plastibot/citro/images/Citro6_32.png

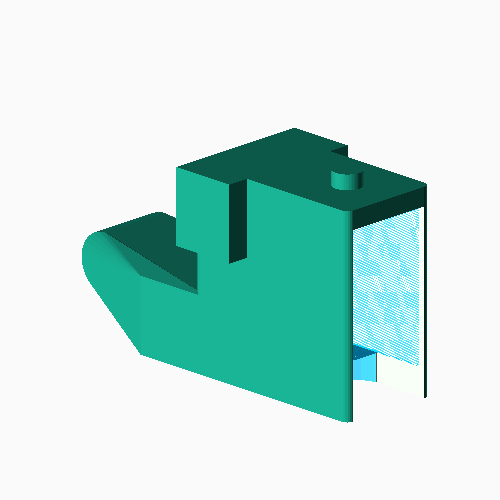
images/Citro6_32.png
