plastibot/citro/images/Citro6_33.png

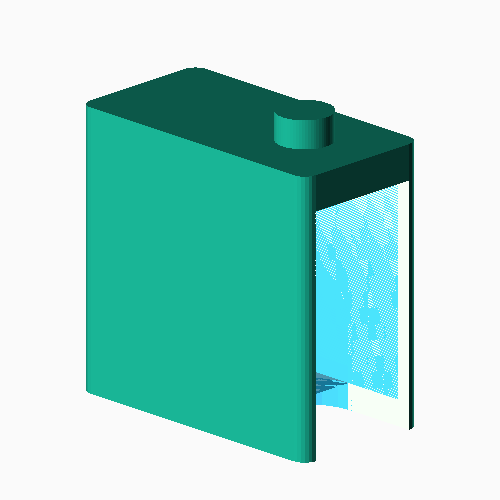
images/Citro6_33.png
