plastibot/citro/images/servo_5g.png

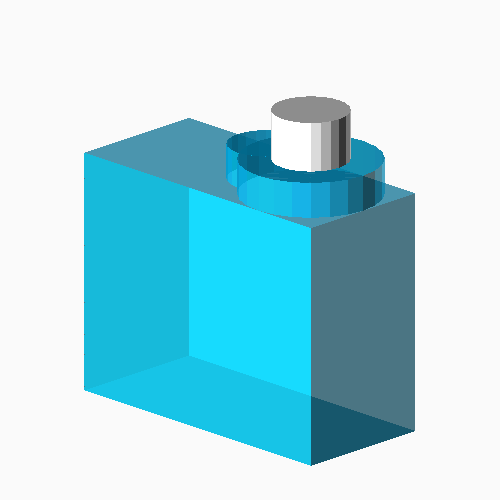
images/servo_5g.png
