plastibot/citro/stl/wemos_d1_mini_pro_board.stl

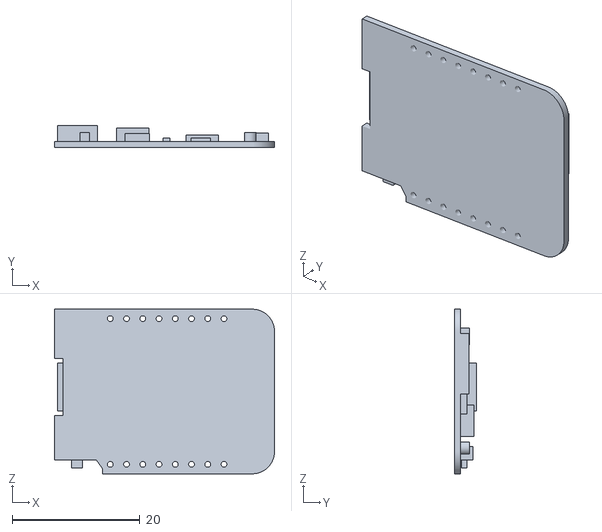
[picture p86: CAD file, 2018-08-11]
stl/wemos_d1_mini_pro_board.stl
34.4 x 3.50 x 25.7
