plastibot/citro/MiniPlan6/MiniPlan6_61R.stl

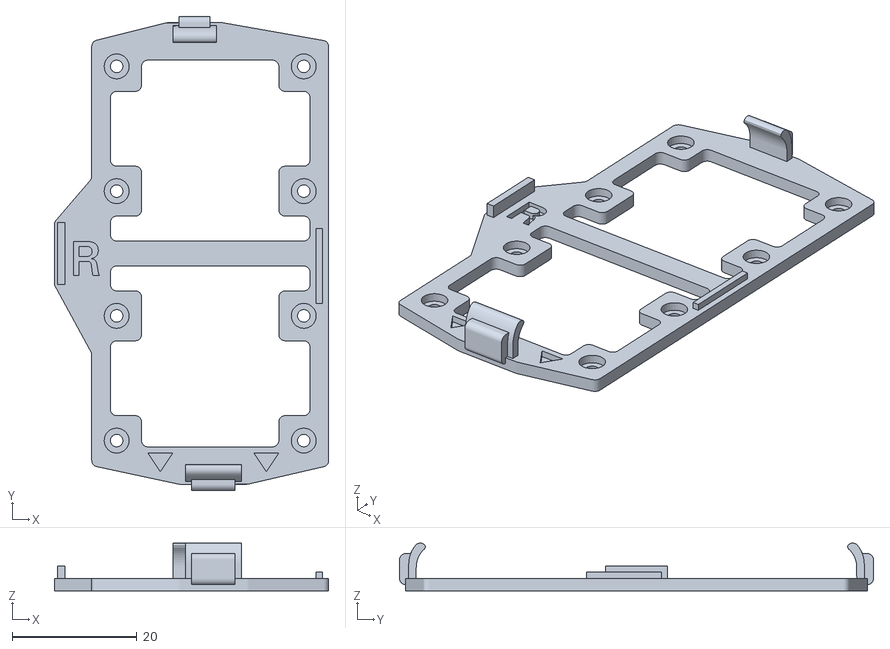
[picture p87: CAD file, 2017-10-25]
MiniPlan6/MiniPlan6_61R.stl
44.0 x 76.0 x 7.67
