plastibot/citro/stl/electronics_pca9685.stl

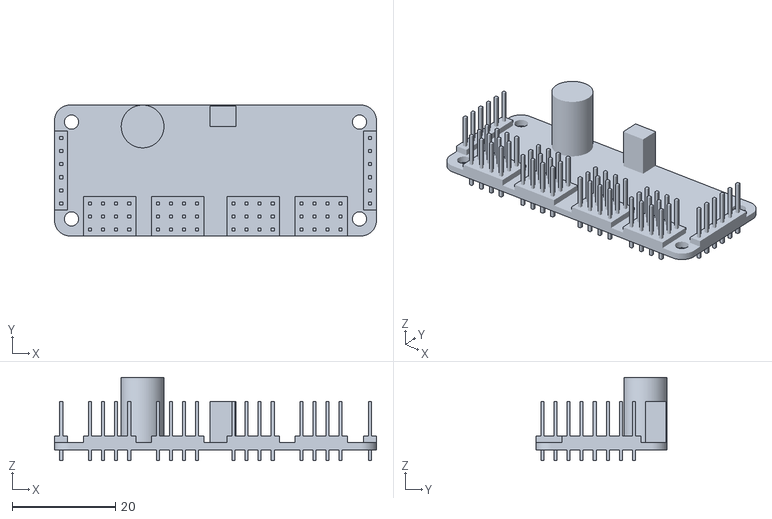
[picture p88: CAD file, 2017-10-30]
stl/electronics_pca9685.stl
62.5 x 25.4 x 16.2
