plastibot/citro/MiniPlan6/MiniPlan6_60.stl

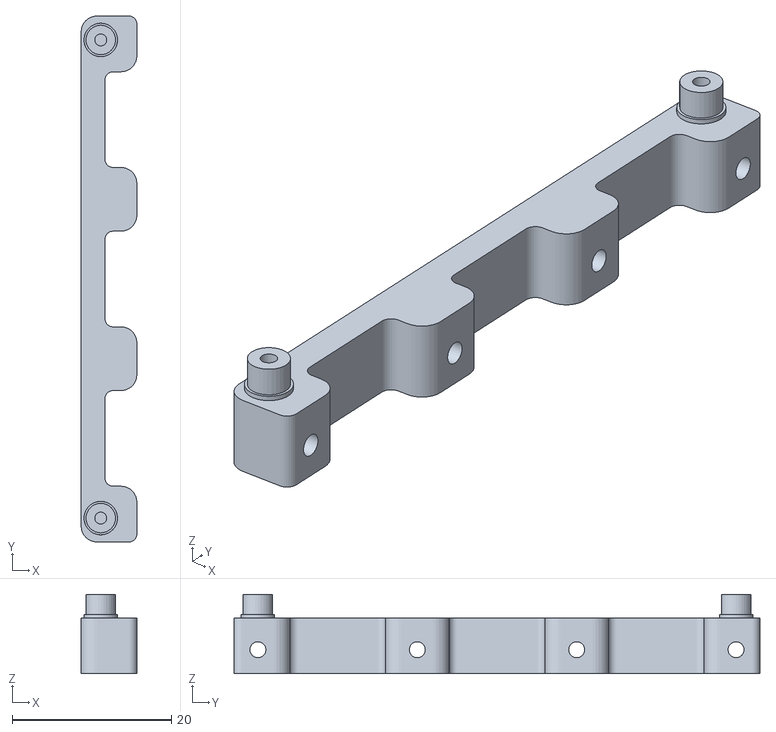
[picture p89: CAD file, 2017-10-25]
MiniPlan6/MiniPlan6_60.stl
7.00 x 66.0 x 9.95
