plastibot/citro/MiniPlan6/MiniPlan6_43R.stl

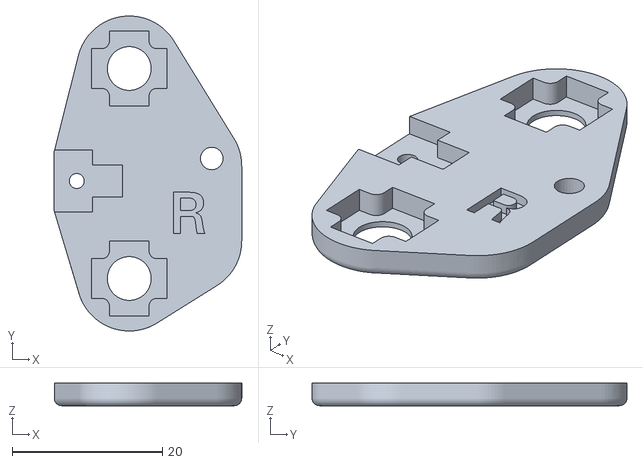
[picture p90: CAD file, 2017-10-25]
MiniPlan6/MiniPlan6_43R.stl
25.0 x 42.0 x 3.00
