plastibot/citro/stl/Citro6_32.stl

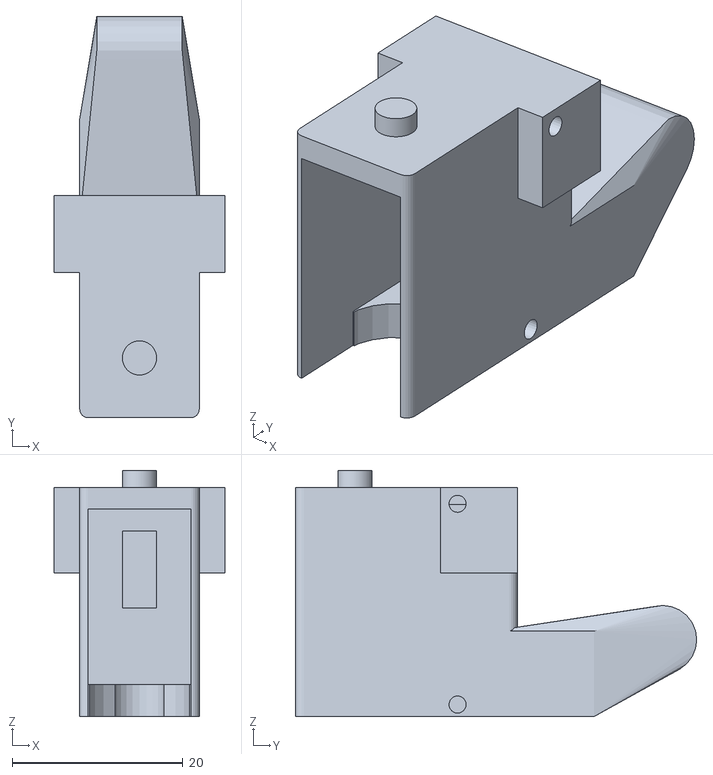
[picture p91: CAD file, 2017-10-30]
stl/Citro6_32.stl
20.0 x 47.0 x 28.8
