plastibot/citro/stl/Citro6_43L.stl

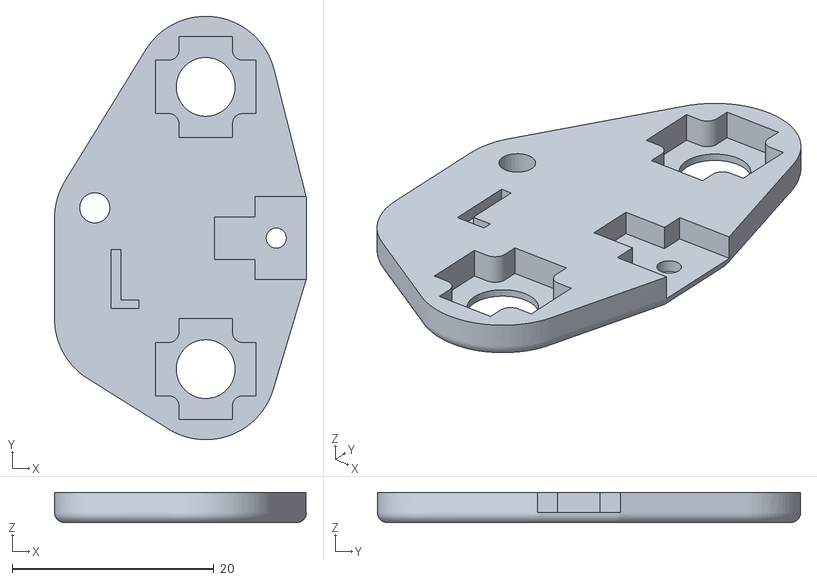
[picture p92: CAD file, 2017-10-30]
stl/Citro6_43L.stl
25.0 x 42.0 x 3.00
