plastibot/citro/MiniPlan6/MiniPlan6_45L.stl

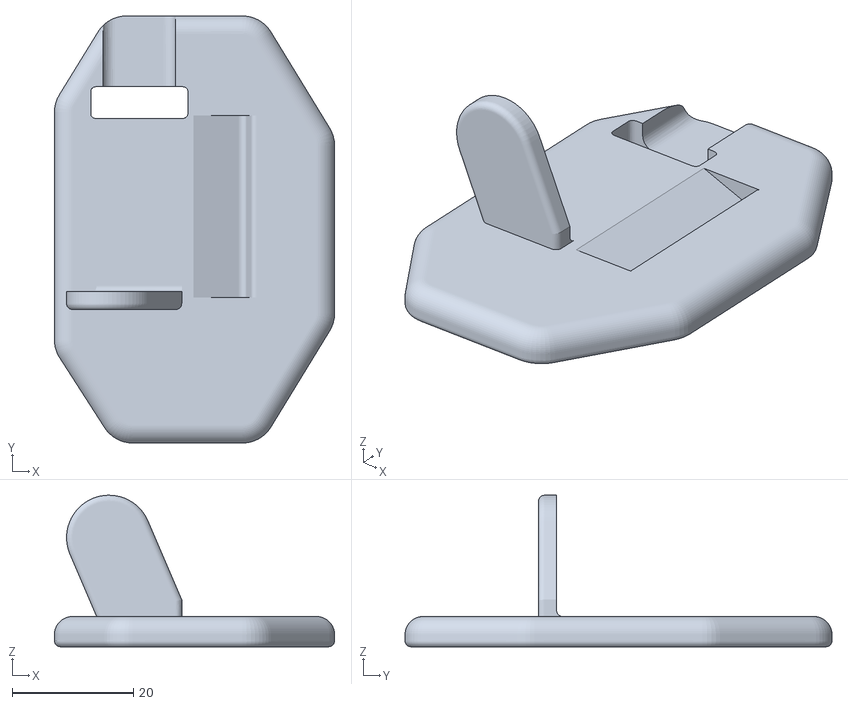
[picture p93: CAD file, 2017-10-25]
MiniPlan6/MiniPlan6_45L.stl
46.2 x 70.4 x 25.0
