plastibot/citro/MiniPlan6/MiniPlan6_40D.stl

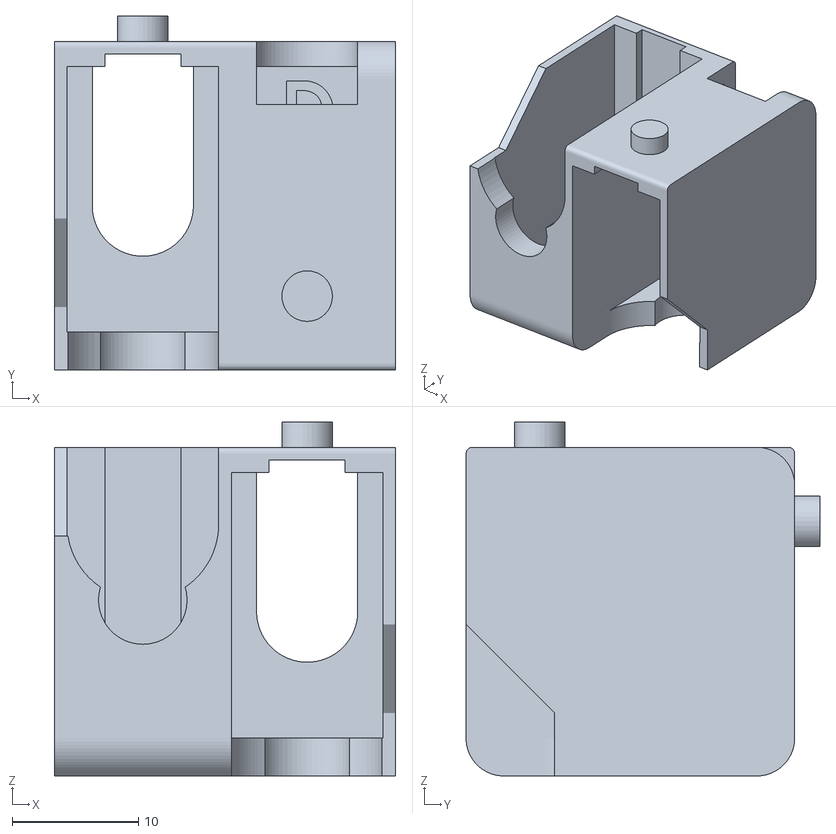
[picture p94: CAD file, 2017-10-25]
MiniPlan6/MiniPlan6_40D.stl
27.0 x 28.0 x 28.0
