plastibot/citro/stl/Citro6_50.stl

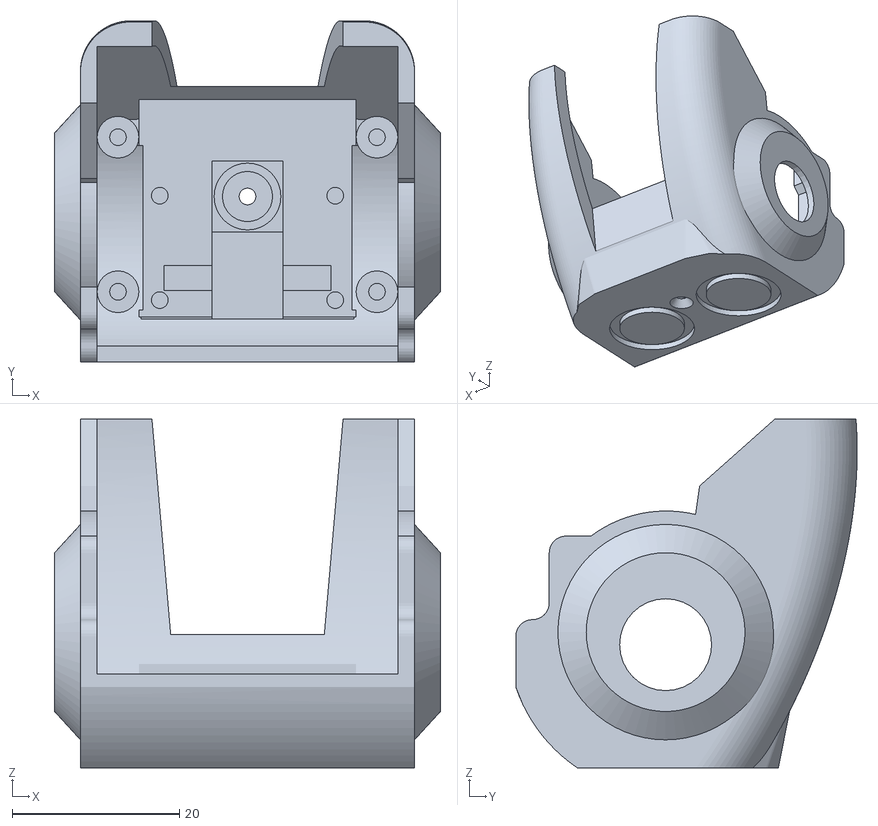
[picture p95: CAD file, 2017-10-30]
stl/Citro6_50.stl
46.2 x 40.9 x 41.8
