plastibot/citro/stl/Citro6_20.stl

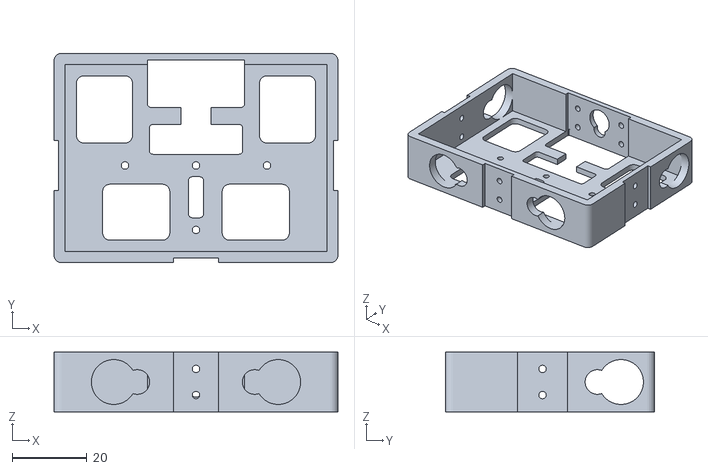
[picture p96: CAD file, 2017-10-30]
stl/Citro6_20.stl
76.0 x 56.0 x 16.0
