plastibot/citro/MiniPlan6/MiniPlan6_70.stl

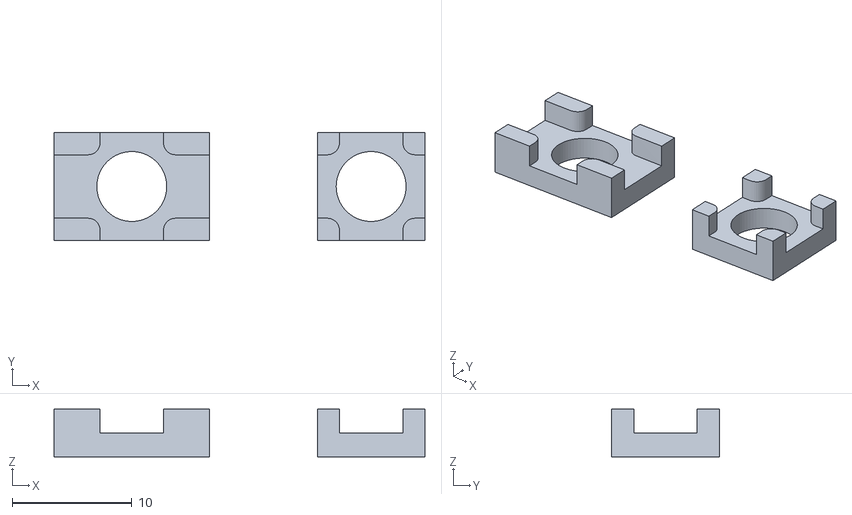
[picture p97: CAD file, 2017-10-25]
MiniPlan6/MiniPlan6_70.stl
31.0 x 9.00 x 4.00
