plastibot/citro/MiniPlan6/MiniPlan5_40.stl

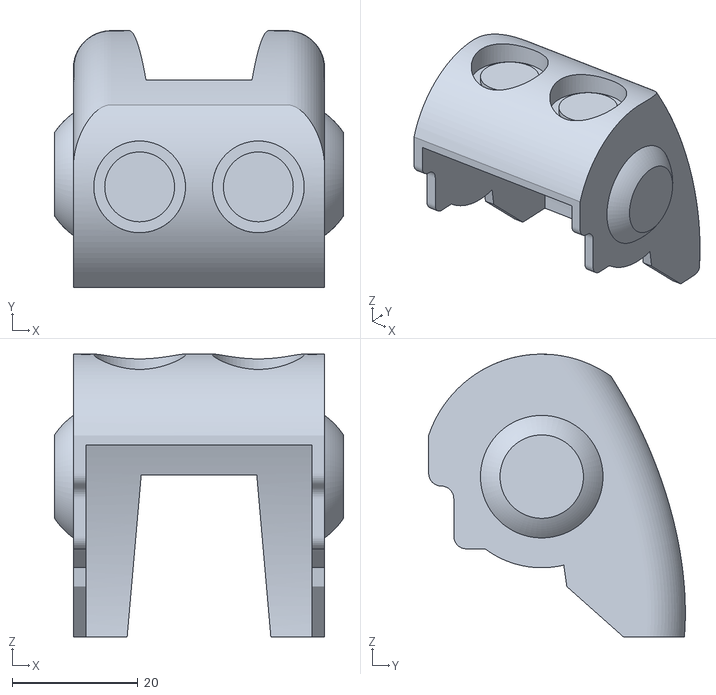
[picture p98: CAD file, 2017-10-25]
MiniPlan6/MiniPlan5_40.stl
46.0 x 40.9 x 45.0
