plastibot/citro/stl/Citro6_51.stl

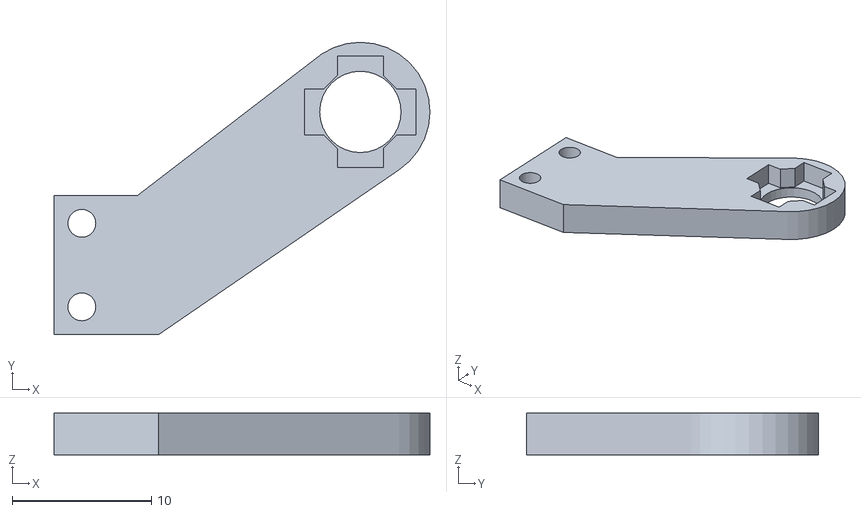
[picture p99: CAD file, 2017-10-30]
stl/Citro6_51.stl
27.0 x 21.0 x 3.00
