plastibot/citro/stl/Citro6_33.stl

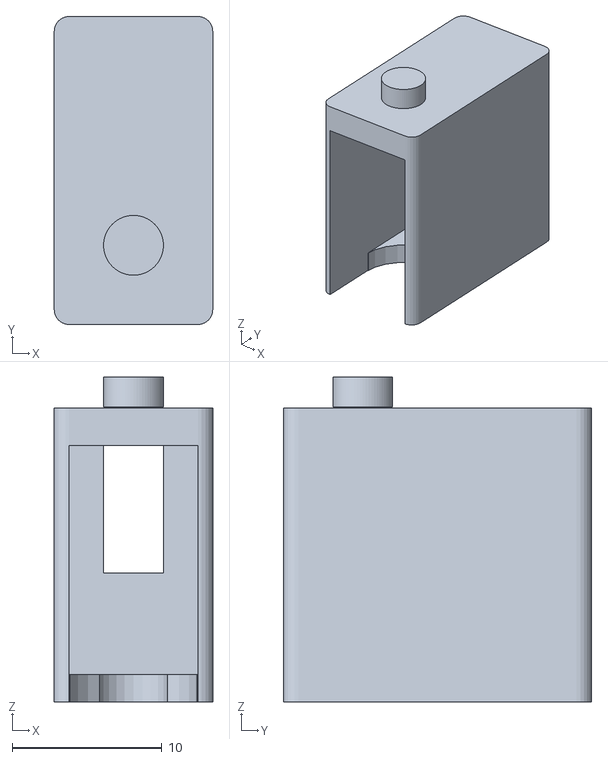
[picture p100: CAD file, 2017-10-30]
stl/Citro6_33.stl
10.6 x 20.6 x 21.7
