plastibot/citro/MiniPlan6/MiniPlan6_30.stl

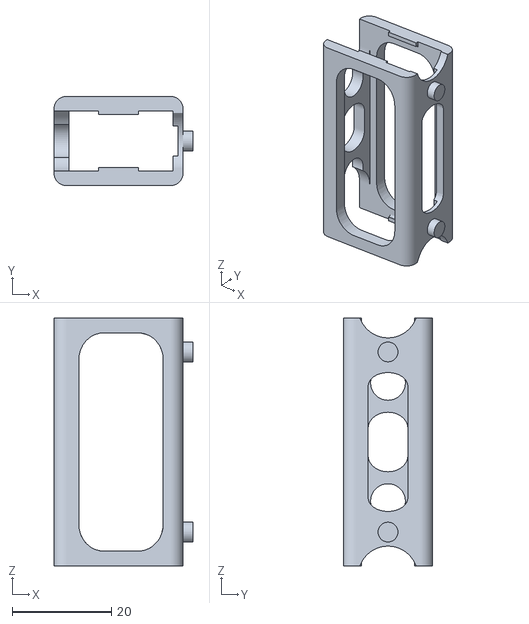
[picture p101: CAD file, 2017-10-25]
MiniPlan6/MiniPlan6_30.stl
28.0 x 18.0 x 50.0
