plastibot/citro/stl/Citro6_40B.stl

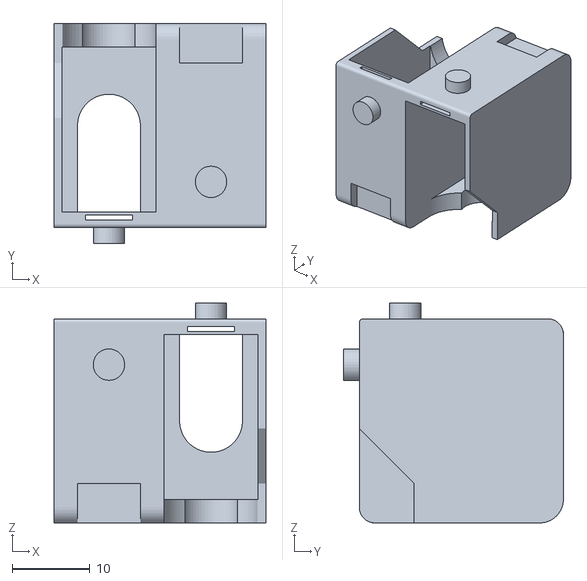
[picture p102: CAD file, 2017-10-30]
stl/Citro6_40B.stl
27.3 x 28.3 x 28.3
