plastibot/citro/stl/Citro6_12B.stl

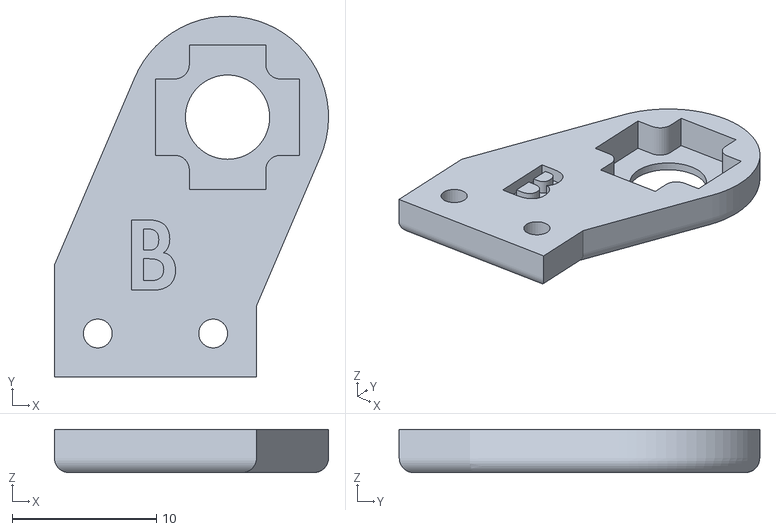
[picture p103: CAD file, 2017-10-30]
stl/Citro6_12B.stl
19.0 x 25.0 x 3.00
