plastibot/citro/stl/Citro6_26.stl

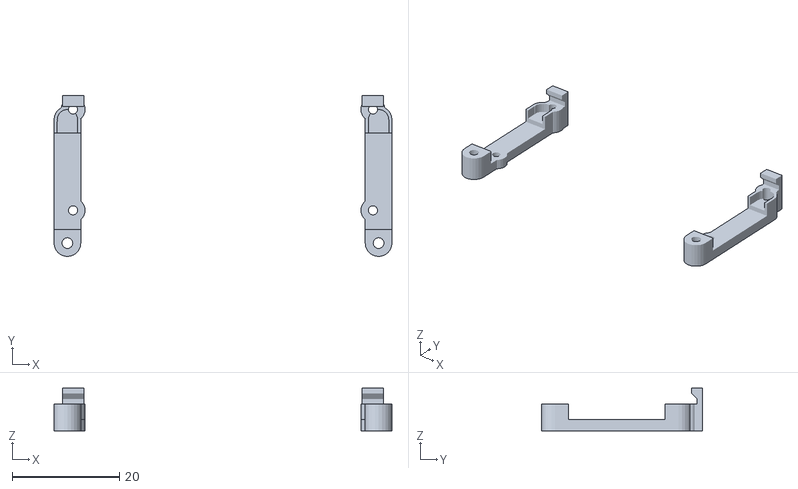
[picture p104: CAD file, 2017-10-30]
stl/Citro6_26.stl
63.0 x 30.0 x 8.00
