plastibot/citro/stl/Citro6_22.stl

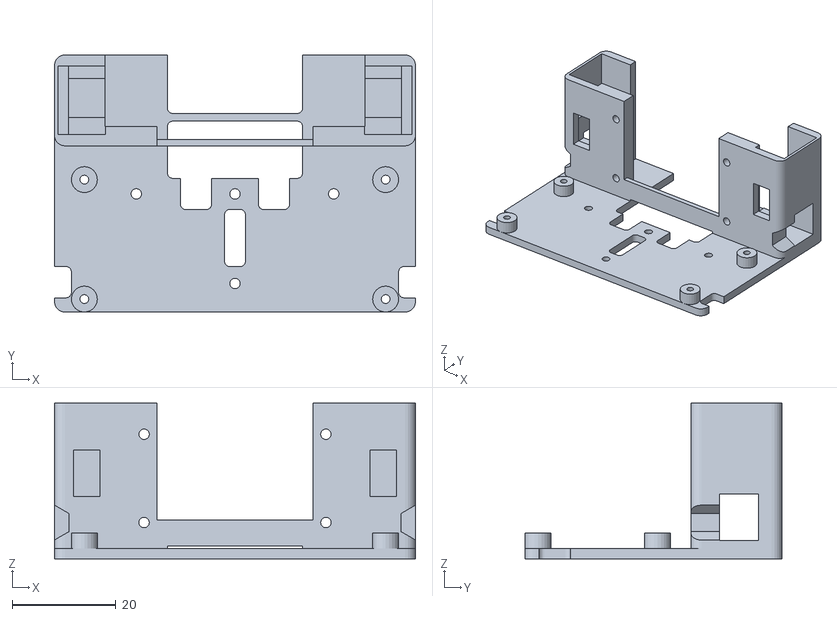
[picture p105: CAD file, 2017-10-30]
stl/Citro6_22.stl
69.5 x 49.5 x 30.0
