plastibot/citro/stl/servo_5g.stl

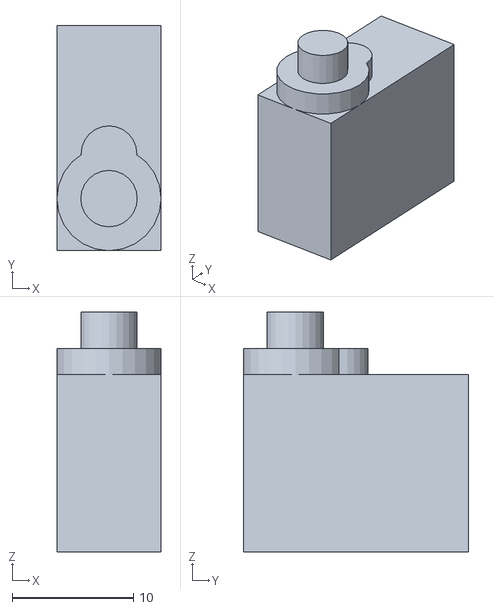
[picture p106: CAD file, 2017-10-30]
stl/servo_5g.stl
8.60 x 18.6 x 19.8
