plastibot/citro/stl/electronics_PiCamera.stl

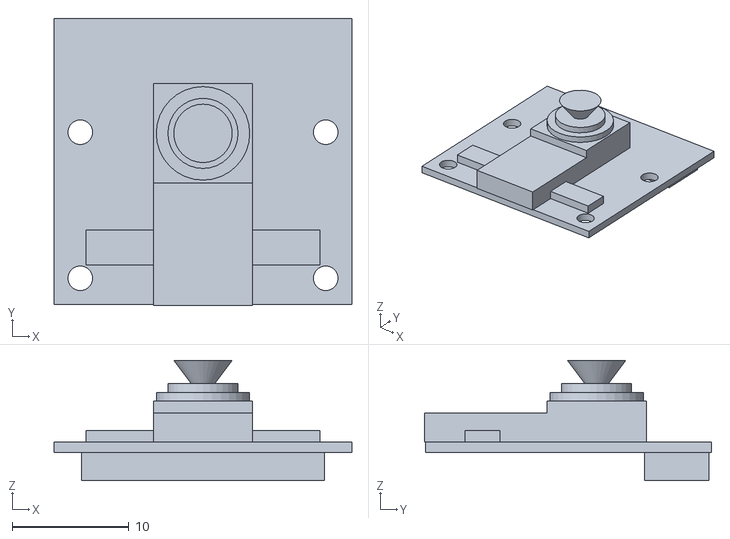
[picture p107: CAD file, 2017-10-30]
stl/electronics_PiCamera.stl
25.5 x 24.6 x 10.3
