plastibot/citro/stl/Citro6_25.stl

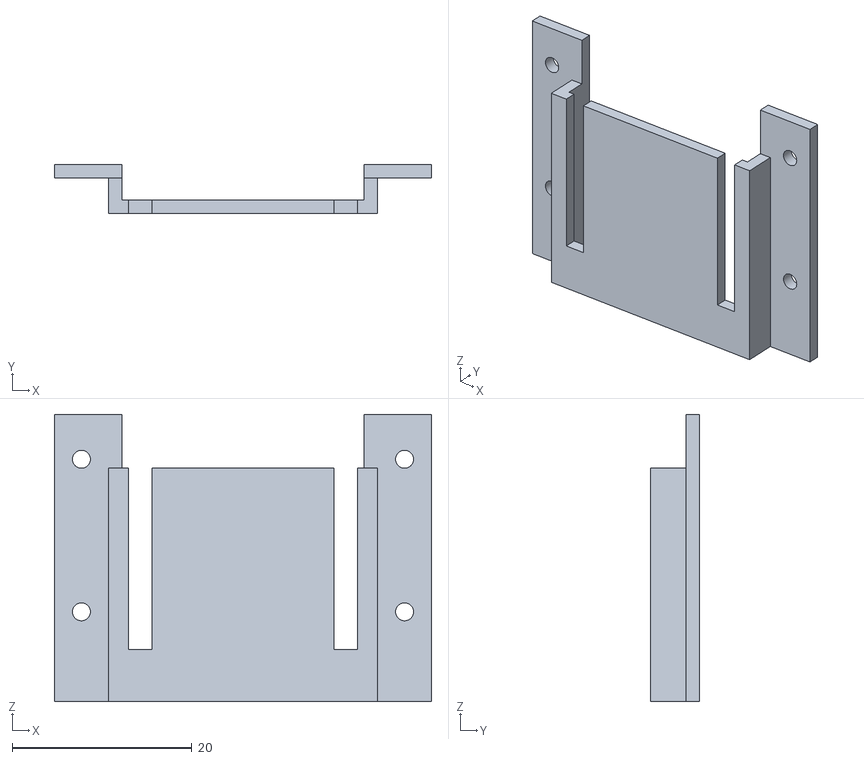
[picture p108: CAD file, 2017-10-30]
stl/Citro6_25.stl
42.0 x 5.50 x 32.0
