plastibot/citro/stl/electronics_PiZero.stl

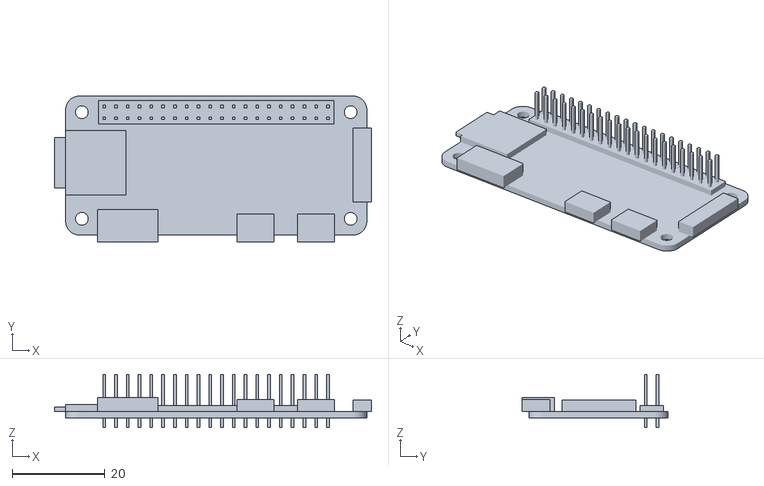
[picture p109: CAD file, 2017-10-30]
stl/electronics_PiZero.stl
68.4 x 31.5 x 11.5
