plastibot/citro/stl/Citro6_27.stl

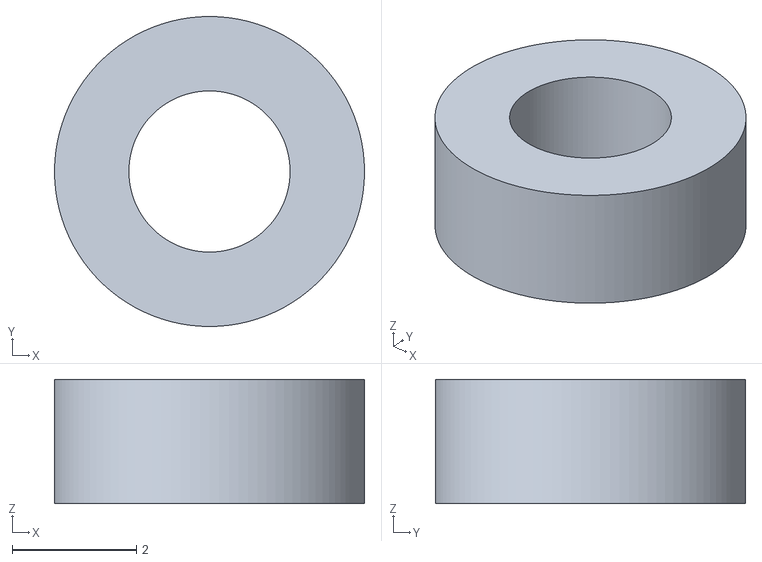
[picture p110: CAD file, 2017-10-30]
stl/Citro6_27.stl
5.00 x 5.00 x 2.00
