plastibot/citro/stl/servo_12g.stl

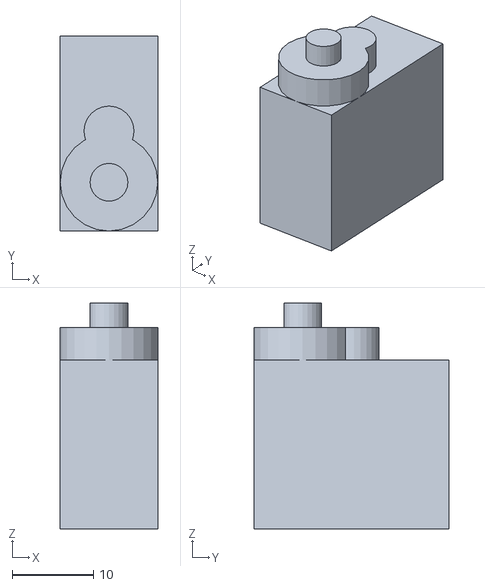
[picture p111: CAD file, 2017-10-30]
stl/servo_12g.stl
12.0 x 24.0 x 27.8
