plastibot/citro/stl/Citro6_53.stl

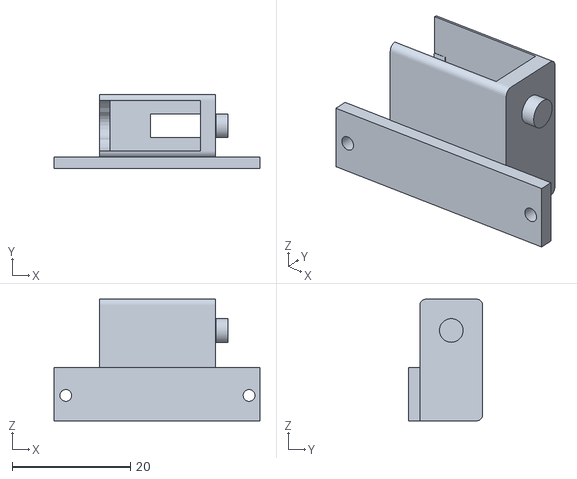
[picture p112: CAD file, 2017-10-30]
stl/Citro6_53.stl
34.9 x 12.6 x 20.6
