plastibot/citro/stl/Citro6_52.stl

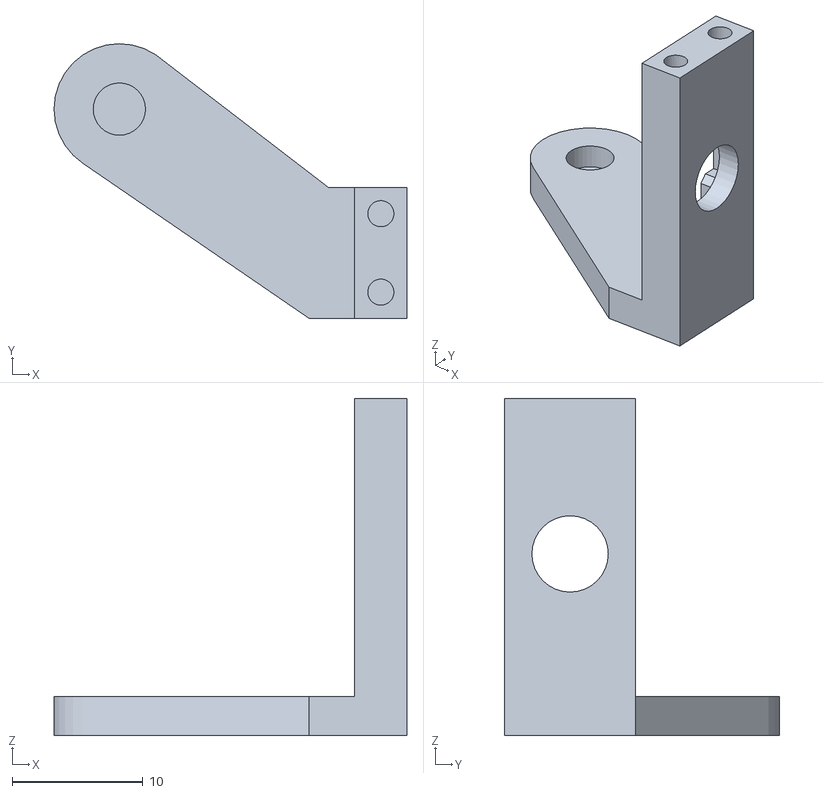
[picture p113: CAD file, 2017-10-30]
stl/Citro6_52.stl
27.0 x 21.0 x 25.8
