plastibot/citro/stl/Citro6_23.stl

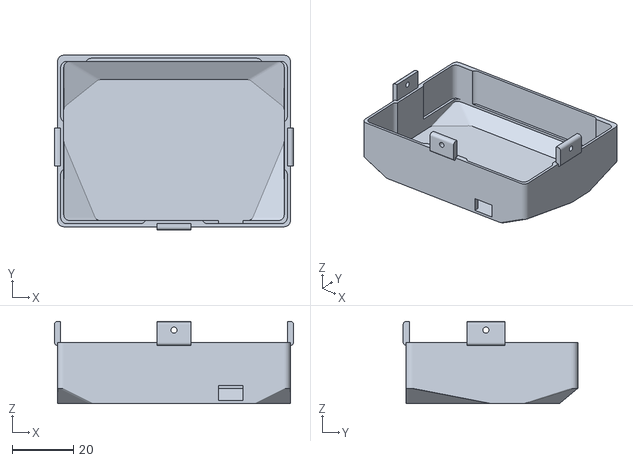
[picture p114: CAD file, 2017-10-30]
stl/Citro6_23.stl
78.0 x 57.0 x 26.9
