plastibot/citro/stl/Citro6_21.stl

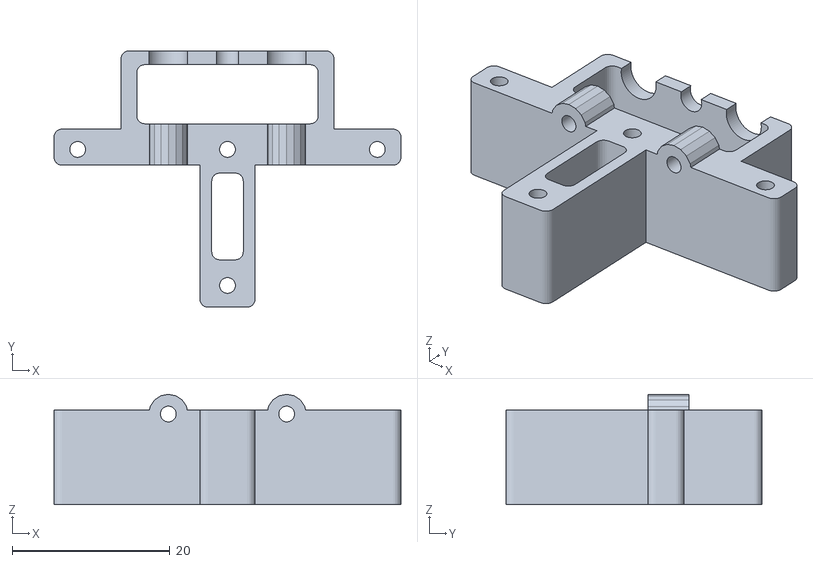
[picture p115: CAD file, 2017-10-30]
stl/Citro6_21.stl
44.0 x 32.5 x 14.0
