plastibot/citro/stl/electronics_dc_dc.stl

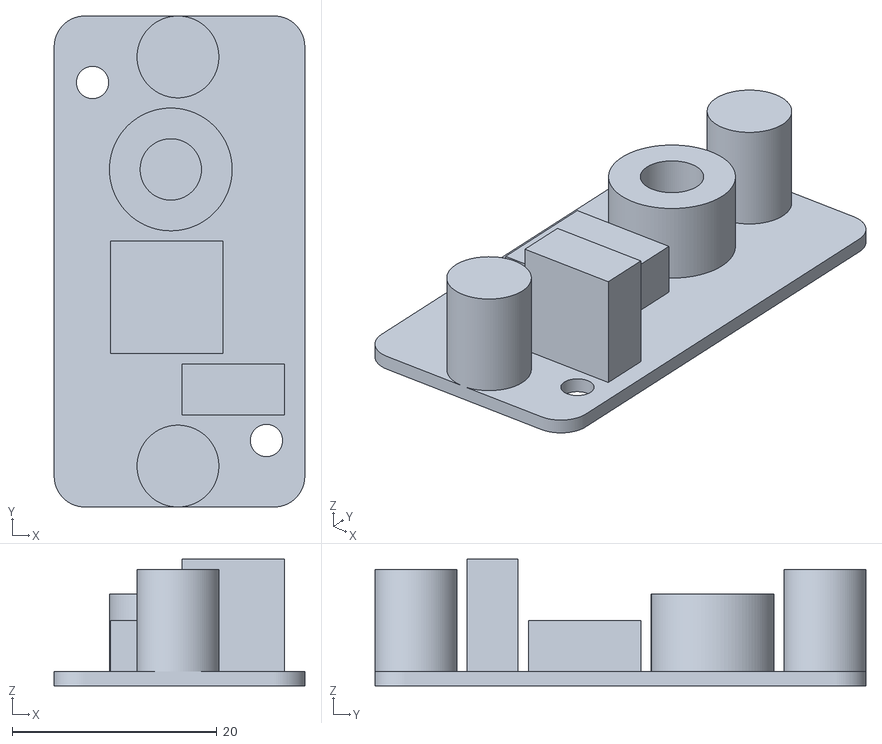
[picture p116: CAD file, 2017-10-30]
stl/electronics_dc_dc.stl
24.5 x 48.0 x 12.4
