plastibot/citro/stl/Citro6_40_mod.stl

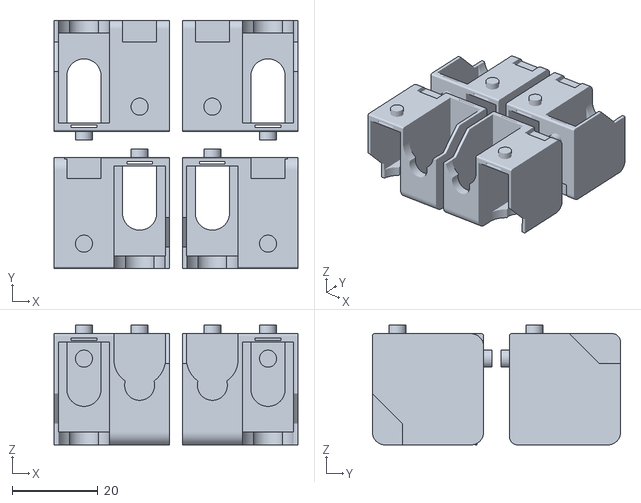
[picture p117: CAD file, 2017-10-25]
stl/Citro6_40_mod.stl
57.0 x 58.0 x 28.0
