plastibot/citro/openscad/servo_5g.scad

include <Config.scad>

servo_5g();


$fn = 24;
//x,y,z => l,w,h


module servo_5g() {
  
    translate([-servo5_l/2, -servo5_w/2, -body5_h/2-hub5_h/2-horn5_h/2]) {
    
        color("white") 
        translate([servo5_l/2,servo5_l/2,body5_h+hub5_h])
        cylinder(r=horn5_r,h=horn5_h);
        
        color("deepSkyBlue",.7) //deepSkyBlue
        union() {
            cube([servo5_l,servo5_w,body5_h]);
            translate([servo5_l/2,servo5_l/2,body5_h])
            cylinder(r=servo5_l/2,h=hub5_h);
            translate([servo5_l/2,servo5_l/2+3.7,body5_h])
            cylinder(r=small_hub5_r,h=hub5_h);
            
        }
    }
}
