plastibot/citro/openscad/Citro6_11.scad

Citro6_11();

module Citro6_11(){
    
    import("../Miniplan6/MiniPlan6_11.stl", convexity=3);
    
}
