plastibot/citro/openscad/Citro6_12A.scad

Citro6_12A();

module Citro6_12A(){
    
    import("../Miniplan6/MiniPlan6_12A.stl", convexity=3);
    
}
