plastibot/citro/openscad/Citro6_12B.scad

Citro6_12B();

module Citro6_12B(){

    import("../Miniplan6/MiniPlan6_12B.stl", convexity=3);
    
}
