plastibot/citro/openscad/Citro6_13A.scad

Citro6_13A();

module Citro6_13A(){
    
    import("../Miniplan6/MiniPlan6_13A.stl", convexity=3);
    
}
