plastibot/citro/openscad/Citro6_13B.scad

Citro6_13B();

module Citro6_13B(){
    
    import("../Miniplan6/MiniPlan6_13B.stl", convexity=3);
    
}
