plastibot/citro/openscad/Citro6_30.scad

Citro6_30();

module Citro6_30(){

    import("../Miniplan6/MiniPlan6_30.stl", convexity=3);
    
}
