plastibot/citro/openscad/Citro6_31L.scad

Citro6_31L();

module Citro6_31L(){
    
    import("../Miniplan6/MiniPlan6_31L.stl", convexity=3);
    
}
