plastibot/citro/openscad/Citro6_31R.scad

Citro6_31R();

module Citro6_31R(){

    import("../Miniplan6/MiniPlan6_31R.stl", convexity=3);
    
}
