plastibot/citro/openscad/Citro6_41L.scad

Citro6_41L();

module Citro6_41L(){
    
    import("../Miniplan6/MiniPlan6_41L.stl", convexity=3);
    
}
