plastibot/citro/openscad/Citro6_41R.scad

Citro6_41R();

module Citro6_41R(){
    
    import("../Miniplan6/MiniPlan6_41R.stl", convexity=3);
    
}
