plastibot/citro/openscad/Citro6_42.scad

Citro6_42();

module Citro6_42(){
    
    import("../Miniplan6/MiniPlan6_42.stl", convexity=3);
    
}
