plastibot/citro/openscad/Citro6_43L.scad

Citro6_43L();

module Citro6_43L(){
    
    import("../Miniplan6/MiniPlan6_43L.stl", convexity=3);
    
}
