plastibot/citro/openscad/Citro6_43R.scad

Citro6_43R();

module Citro6_43R(){

    import("../Miniplan6/MiniPlan6_43R.stl", convexity=3);
    
}
