plastibot/citro/openscad/Citro6_44L.scad

Citro6_44L();

module Citro6_44L(){

    import("../Miniplan6/MiniPlan6_44L.stl", convexity=3);
    
}
