plastibot/citro/openscad/Citro6_44R.scad

Citro6_44R();

module Citro6_44R(){

    import("../Miniplan6/MiniPlan6_44R.stl", convexity=3);
    
}
