plastibot/citro/openscad/Citro6_45L.scad

Citro6_45L();

module Citro6_45L(){
    
    import("../Miniplan6/MiniPlan6_45L.stl", convexity=3);
    
}
