plastibot/citro/openscad/Citro6_45R.scad

Citro6_45R();

module Citro6_45R(){

    import("../Miniplan6/MiniPlan6_45R.stl", convexity=3);
    
}
