plastibot/citro/openscad/Citro6_54.scad

include <Config.scad>
use <servo_12g.scad>
use <servo_5g.scad>
use <electronics.scad>


Citro6_54();


module Citro6_54(){

            
            translate([0,0,0])
            //color("red")
            import("../MiniPlan6/MiniPlan51_70.stl", convexity=3);
            

}
