plastibot/citro/openscad/Citro6_60.scad

import("../Miniplan6/MiniPlan6_60.stl", convexity=3);
