plastibot/citro/openscad/Citro6_61L.scad

import("../Miniplan6/MiniPlan6_61L.stl", convexity=3);
