plastibot/citro/openscad/Citro6_61R.scad

import("../Miniplan6/MiniPlan6_61R.stl", convexity=3);
