plastibot/citro/openscad/Citro6_70.scad

import("../Miniplan6/MiniPlan6_70.stl", convexity=3);
